GadgetUK164/Marine/20250608_175438.jpg

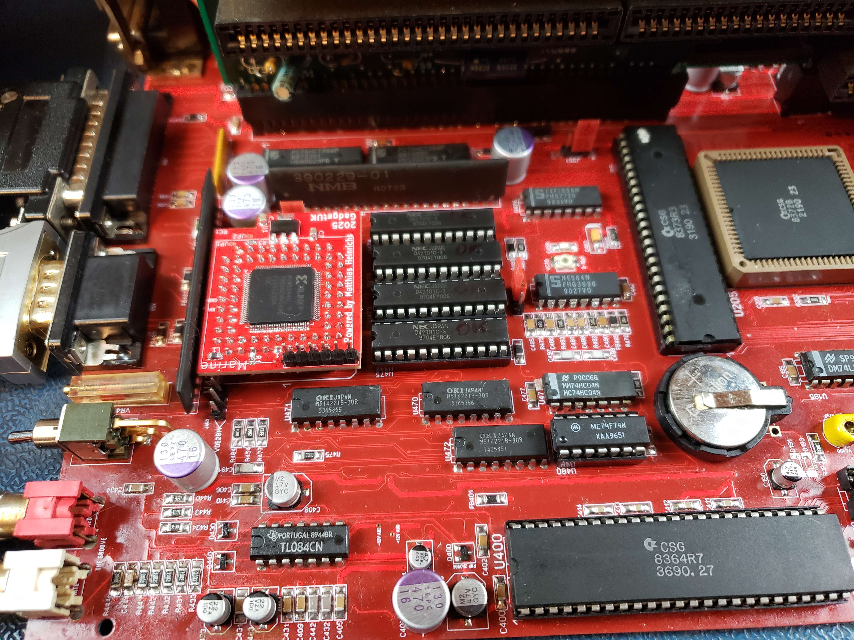
20250608_175438.jpg
